a5632645/HSDAC/HID-Bootloader/Peripheral/inc/ch32v30x_tim.h

/********************************** (C) COPYRIGHT  *******************************
* File Name          : ch32v30x_tim.h
* Author             : WCH
* Version            : V1.0.0
* Date               : 2021/06/06
* Description        : This file contains all the functions prototypes for the  
*                      TIM firmware library.
*********************************************************************************
* Copyright (c) 2021 Nanjing Qinheng Microelectronics Co., Ltd.
* Attention: This software (modified or not) and binary are used for 
* microcontroller manufactured by Nanjing Qinheng Microelectronics.
*******************************************************************************/
#ifndef __CH32V30x_TIM_H
#define __CH32V30x_TIM_H

#ifdef __cplusplus
 extern "C" {
#endif

#include "ch32v30x.h"

/* TIM Time Base Init structure definition */
typedef struct
{
  uint16_t TIM_Prescaler;         /* Specifies the prescaler value used to divide the TIM clock.
                                     This parameter can be a number between 0x0000 and 0xFFFF */

  uint16_t TIM_CounterMode;       /* Specifies the counter mode.
                                     This parameter can be a value of @ref TIM_Counter_Mode */

  uint16_t TIM_Period;            /* Specifies the period value to be loaded into the active
                                     Auto-Reload Register at the next update event.
                                     This parameter must be a number between 0x0000 and 0xFFFF.  */ 

  uint16_t TIM_ClockDivision;     /* Specifies the clock division.
                                    This parameter can be a value of @ref TIM_Clock_Division_CKD */

  uint8_t TIM_RepetitionCounter;  /* Specifies the repetition counter value. Each time the RCR downcounter
                                     reaches zero, an update event is generated and counting restarts
                                     from the RCR value (N).
                                     This means in PWM mode that (N+1) corresponds to:
                                        - the number of PWM periods in edge-aligned mode
                                        - the number of half PWM period in center-aligned mode
                                     This parameter must be a number between 0x00 and 0xFF. 
                                     @note This parameter is valid only for TIM1 and TIM8. */
} TIM_TimeBaseInitTypeDef;       

/* TIM Output Compare Init structure definition */
typedef struct
{
  uint16_t TIM_OCMode;        /* Specifies the TIM mode.
                                 This parameter can be a value of @ref TIM_Output_Compare_and_PWM_modes */

  uint16_t TIM_OutputState;   /* Specifies the TIM Output Compare state.
                                 This parameter can be a value of @ref TIM_Output_Compare_state */

  uint16_t TIM_OutputNState;  /* Specifies the TIM complementary Output Compare state.
                                 This parameter can be a value of @ref TIM_Output_Compare_N_state
                                 @note This parameter is valid only for TIM1 and TIM8. */

  uint16_t TIM_Pulse;         /* Specifies the pulse value to be loaded into the Capture Compare Register. 
                                 This parameter can be a number between 0x0000 and 0xFFFF */

  uint16_t TIM_OCPolarity;    /* Specifies the output polarity.
                                 This parameter can be a value of @ref TIM_Output_Compare_Polarity */

  uint16_t TIM_OCNPolarity;   /* Specifies the complementary output polarity.
                                 This parameter can be a value of @ref TIM_Output_Compare_N_Polarity
                                 @note This parameter is valid only for TIM1 and TIM8. */

  uint16_t TIM_OCIdleState;   /* Specifies the TIM Output Compare pin state during Idle state.
                                 This parameter can be a value of @ref TIM_Output_Compare_Idle_State
                                 @note This parameter is valid only for TIM1 and TIM8. */

  uint16_t TIM_OCNIdleState;  /* Specifies the TIM Output Compare pin state during Idle state.
                                 This parameter can be a value of @ref TIM_Output_Compare_N_Idle_State
                                 @note This parameter is valid only for TIM1 and TIM8. */
} TIM_OCInitTypeDef;
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
